MityusPityus/Umwelt-Messgeraet/assets/doku-bild-1.jpg

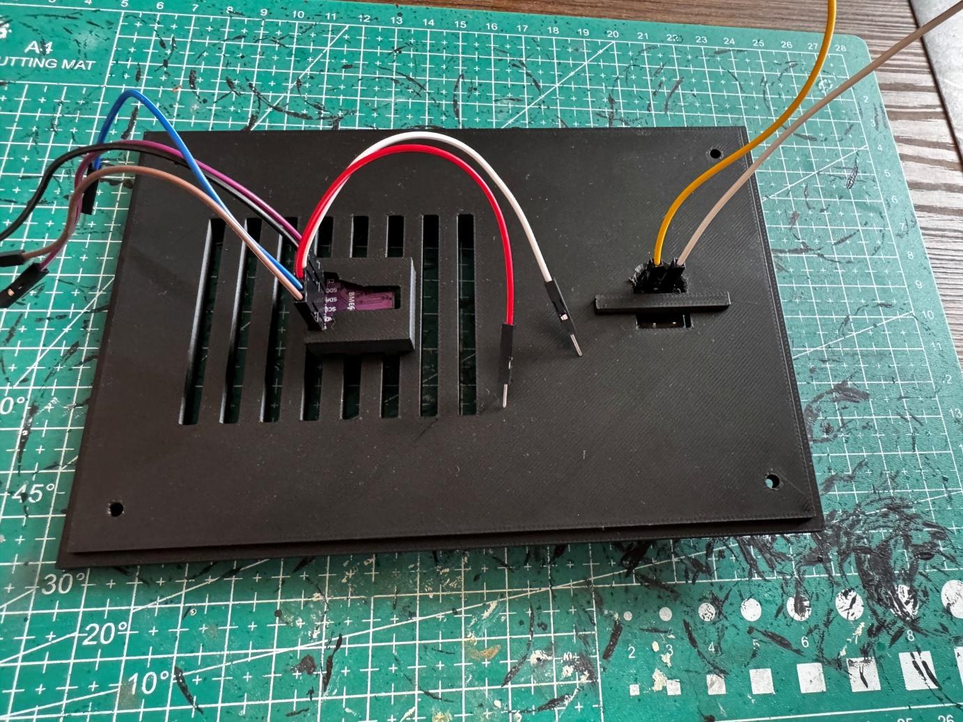
assets/doku-bild-1.jpg
